phl025/ESP32_RC_Controller/document/pictures/ESP32_RC_Controler_004.jpg

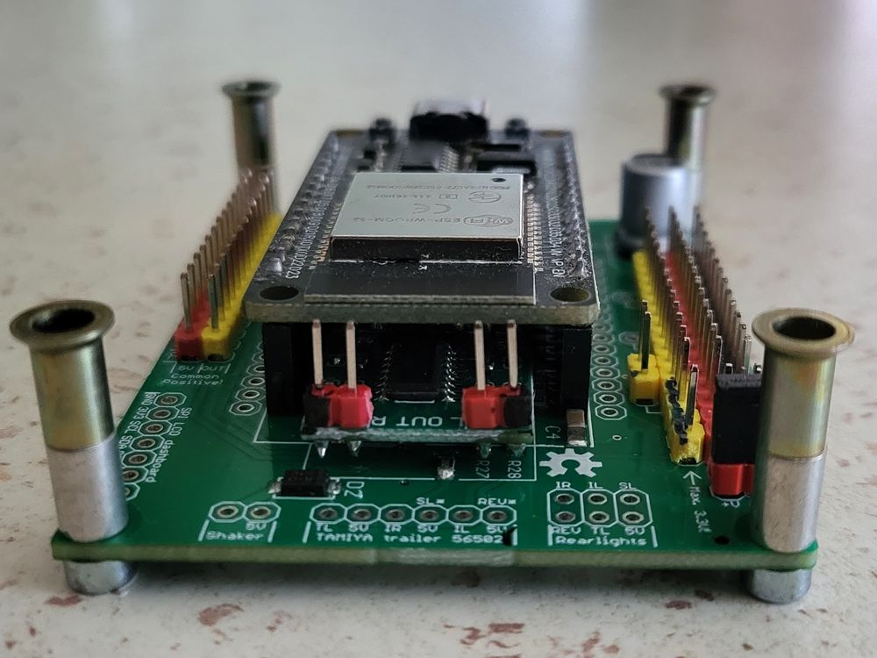
document/pictures/ESP32_RC_Controler_004.jpg
