phl025/ESP32_RC_Controller/document/pictures/ESP32_RC_Controler_006.jpg

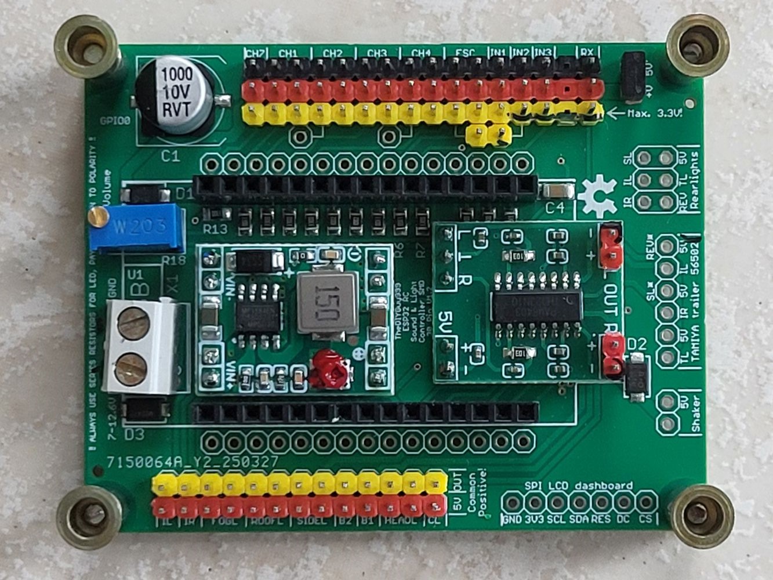
document/pictures/ESP32_RC_Controler_006.jpg
