phl025/ESP32_RC_Controller/src/src_ext/dashboard_frevic.h

#include "Arduino.h"
#include <TFT_eSPI.h>   // https://github.com/Bodmer/TFT_eSPI

/*
 * dashboard.h - Library to drive a 80x160px color LCD as rc truck dashboard
 *
 * https://github.com/Gamadril/Rc_Engine_Sound_ESP32
 * MIT License
 */

#ifndef DASHBOARD_H_FREVIC
#define DASHBOARD_H_FREVIC

#define SCREEN_WIDTH 160
#define SCREEN_HEIGHT 80

#define purple 0xEA16

// DEFINICIONES FREDY
#define SILVER 0xC618

#define FRAME_MAIN_X 80
#define FRAME_MAIN_Y 2
#define FRAME_MAIN_WITH 30
#define FRAME_MAIN_HEITH 14

#define FRAME_SUBMAIN_X 80
#define FRAME_SUBMAIN_Y 67
#define FRAME_SUBMAIN_WITH 60
#define FRAME_SUBMAIN_HEITH 12

#define INSTRUMENTOS_Y SCREEN_HEIGHT - 10;

#define GEAR_BOX_X 80
#define GEAR_BOX_Y 3 //(SCREEN_HEIGHT / 2) - 2
#define GEAR_BOX_WITH 12
#define GEAR_BOX_HEITH 20

// FIN DEFINICIONES FREDY

#define DEG2RAD 0.0174532925
#define SPEED_MIN 0
#define SPEED_MAX 120
#define RPM_MIN 0
#define RPM_MAX 500
#define FUEL_MIN 0
#define FUEL_MAX 100
#define ADBLUE_MIN 0
#define ADBLUE_MAX 100

#define SPEED_CIRCLE_CENTER_X 36
#define SPEED_CIRCLE_CENTER_Y 40
#define SPEED_CIRCLE_RADIUS 37
#define SPEED_NEEDLE_LENGTH 20
#define SPEED_CIRCLE_ANGLE_START -215 // -180 - 45
#define SPEED_CIRCLE_SEGMENTS 12
#define SPEED_CIRCLE_SEGMENT_ANGLE 20.83
#define SPEED_CIRCLE_ANGLE_END 35

#define RPM_CIRCLE_CENTER_X SCREEN_WIDTH - SPEED_CIRCLE_CENTER_X - 1
#define RPM_CIRCLE_CENTER_Y SPEED_CIRCLE_CENTER_Y
#define RPM_CIRCLE_RADIUS SPEED_CIRCLE_RADIUS
#define RPM_CIRCLE_ANGLE_START SPEED_CIRCLE_ANGLE_START
#define RPM_CIRCLE_SEGMENTS 12
#define RPM_CIRCLE_SEGMENT_ANGLE 20.83
#define RPM_CIRCLE_ANGLE_END 35

// no aplican
#define FUEL_CIRCLE_CENTER_X 30
#define FUEL_CIRCLE_CENTER_Y 60
#define FUEL_CIRCLE_RADIUS 14
#define FUEL_CIRCLE_ANGLE_START -202 // -180 - 22
#define FUEL_CIRCLE_SEGMENTS 16
#define FUEL_CIRCLE_SEGMENT_ANGLE 14
#define FUEL_CIRCLE_ANGLE_END \
    FUEL_CIRCLE_ANGLE_START + FUEL_CIRCLE_SEGMENTS *FUEL_CIRCLE_SEGMENT_ANGLE

#define ADBLUE_CIRCLE_CENTER_X SCREEN_WIDTH - 30
#define ADBLUE_CIRCLE_CENTER_Y 60
#define ADBLUE_CIRCLE_RADIUS 14
#define ADBLUE_CIRCLE_ANGLE_START -202 // -180 - 22
#define ADBLUE_CIRCLE_SEGMENTS 16
#define ADBLUE_CIRCLE_SEGMENT_ANGLE 14
#define ADBLUE_CIRCLE_ANGLE_END \
    ADBLUE_CIRCLE_ANGLE_START + ADBLUE_CIRCLE_SEGMENTS *ADBLUE_CIRCLE_SEGMENT_ANGLE

// #define INDICATOR_LEFT_CENTER_X SCREEN_WIDTH / 2 - 20
// #define INDICATOR_LEFT_CENTER_Y 9
// #define INDICATOR_RIGHT_CENTER_X SCREEN_WIDTH / 2 + 20
// #define INDICATOR_RIGHT_CENTER_Y 9
// Fredy
#define INDICATOR_LEFT_CENTER_X SCREEN_WIDTH / 2 - 14
#define INDICATOR_LEFT_CENTER_Y 7 // 8

#define INDICATOR_RIGHT_CENTER_X SCREEN_WIDTH / 2 + 14
#define INDICATOR_RIGHT_CENTER_Y 7 // 8

// CUSTOM COLOR DEFINITIONS
// http://www.rinkydinkelectronics.com/calc_rgb565.php
#define offColor 0x2104 // indicators off (very dark grey)
#define backColor 0x0026
#define gaugeColor 0x055D
#define dataColor 0x0311
#define purple 0xEA16
#define needleColor 0xfa29 //The color of the speed and RPM indicator needles (light red for better visibility)

const uint8_t LOW_BEAM_ICON[7][13] PROGMEM = {
    {1, 1, 0, 0, 0, 0, 0, 0, 0, 0, 0, 1, 1},
    {0, 1, 1, 1, 1, 0, 0, 0, 1, 1, 1, 1, 0},
    {0, 0, 1, 0, 1, 1, 0, 1, 1, 0, 1, 0, 0},
    {1, 1, 1, 0, 0, 1, 0, 1, 0, 0, 1, 1, 1},
    {0, 0, 1, 0, 1, 1, 0, 1, 1, 0, 1, 0, 0},
    {0, 1, 1, 1, 1, 0, 0, 0, 1, 1, 1, 1, 0},
    {1, 1, 0, 0, 0, 0, 0, 0, 0, 0, 0, 1, 1}};

const uint8_t HIGH_BEAM_ICON[7][13] PROGMEM = {
    {0, 0, 0, 0, 0, 0, 0, 1, 1, 1, 1, 0, 0},
    {1, 1, 1, 1, 1, 0, 1, 1, 0, 0, 1, 1, 0},
    {0, 0, 0, 0, 0, 0, 1, 0, 0, 0, 0, 1, 1},
    {1, 1, 1, 1, 1, 0, 1, 0, 0, 0, 0, 0, 1},
    {0, 0, 0, 0, 0, 0, 1, 0, 0, 0, 0, 1, 1},
    {1, 1, 1, 1, 1, 0, 1, 1, 0, 0, 1, 1, 0},
    {0, 0, 0, 0, 0, 0, 0, 1, 1, 1, 1, 0, 0}};

const uint8_t FOG_LIGHT_ICON[7][13] PROGMEM = {
    {0, 0, 0, 1, 1, 0, 0, 1, 1, 1, 1, 0, 0},
    {0, 1, 1, 1, 0, 0, 1, 1, 0, 0, 1, 1, 0},
    {1, 0, 1, 0, 1, 0, 1, 0, 0, 0, 0, 1, 1},
    {0, 1, 1, 1, 0, 0, 1, 0, 0, 0, 0, 0, 1},
    {1, 0, 0, 0, 1, 1, 1, 0, 0, 0, 0, 1, 1},
    {0, 1, 1, 1, 1, 0, 1, 1, 0, 0, 1, 1, 0},
    {1, 0, 1, 0, 0, 0, 0, 1, 1, 1, 1, 0, 0}};

const uint8_t PUMP_ICON[6][7] PROGMEM = {
    {0, 1, 1, 1, 1, 0, 0},
    {0, 1, 0, 0, 1, 1, 0},
    {0, 1, 0, 0, 1, 0, 1},
    {0, 1, 1, 1, 1, 1, 0},
    {0, 1, 1, 1, 1, 0, 0},
    {1, 1, 1, 1, 1, 1, 0}};

/**
 * @brief Class acts as a wrapper around TFT_eSPI routines to draw dashboard elements.
 *
 */
class Dashboard
{
public:
    /**
     * Default constructor
     */
    Dashboard();

    /**
     * Performs initialization of the display, rotates the coordinate system of the screen
     * (0,0) is the upper left corner if the connector is on the top.
     * Draws static dashboard elements and sets all values to 0.
     */
    void init(uint8_t value);

    /**
     * Sets the state of the left turn signal.
     * @param on - true to show the signal, false to deactivate it
     */
    void setLeftIndicator(boolean on);

    /**
     * Sets the state of the right turn signal.
     * @param on - true to show the signal, false to deactivate it
     */
    void setRightIndicator(boolean on);

    /**
     * Sets the state of the low beam lights.
     * @param on - true to show the indicator, false to deactivate it
     */
    void setLowBeamIndicator(boolean on);

    /**
     * Sets the state of the high beam lights.
     * @param on - true to show the indicator, false to deactivate it
     */
    void setHighBeamIndicator(boolean on);

    /**
     * Sets the state of the fog lights.
     * @param on - true to show the indicator, false to deactivate it
     */
    void setFogLightIndicator(boolean on);

    /**
     * Sets the speed to show by rotating the needle to the right position.
     * @param value - speed value between SPEED_MIN and SPEED_MAX
     */
    void setSpeed(uint16_t value);

    /**
     * Sets the RPM to show by rotating the needle to the right position.
     * @param value - RPM value between RPM_MIN and RPM_MAX
     */
    void setRPM(uint16_t value);

    /**
     * Sets the fuel level to show by rotating the needle to the right position.
     * @param value - fuel value between FUEL_MIN and FUEL_MAX
     */
    void setFuelLevel(uint16_t value);

    /**
     * Sets the AdBlue level to show by rotating the needle to the right position.
     * @param value - AdBlue value between ADBLUE_MIN and ADBLUE_MAX
     */
    void setAdBlueLevel(uint16_t value);

    /**
     * Sets the gear to show.
     * @param value - -1 for R, 0 for N, > 0 for gear number
     */
    void setGear(int8_t value);
    void setVolt(float value, float threshold);

private:
    TFT_eSPI _tft = TFT_eSPI();

    void drawFrame();
    void drawArc(int16_t cx, int16_t cy, int16_t r, int16_t deg_start, int16_t deg_end,
                 uint32_t color);
    void drawSep(int16_t cx, int16_t cy, uint16_t len, int16_t deg_pos, uint16_t r, uint32_t color);
    void drawNeedle(int16_t cx, int16_t cy, uint16_t len, int16_t deg_pos, uint16_t radius_holder,
                    uint32_t color_needle);
    void drawLeftIndicator(uint32_t color);
    void drawRightIndicator(uint32_t color);
    void drawLowBeamIndicator(uint32_t color);
    void drawHighBeamIndicator(uint32_t color);
    void drawFogLightIndicator(uint32_t color);
    void drawSpeed(uint16_t value);
    void drawRPM(uint16_t value);
    void drawFuel(uint16_t value);
    void drawAdBlue(uint16_t value);
    void drawPump(uint16_t x, uint16_t y, uint32_t color);
    void drawGear(char gear);
    void drawVolt(float volt, float threshold);

    void drawIndicadorFr(int16_t cx, int16_t cy, uint16_t len, int16_t deg_pos,
                         uint16_t radius_holder, uint32_t color_needle,
                         int16_t deg_pos_ant, uint32_t color_needle_ant, uint16_t pVelocidad);
    void drawNumVel();
    void drawNumrpm();

    void drawLogo(int16_t x, int16_t y, const uint16_t *bitmap, int16_t w, int16_t h); //Frevic logo
    
    uint32_t _BROWN = _tft.color565(160, 115, 71);

    float lx[360]; // text of Speed gaouges
    float ly[360];

    float xf[12]; // text of Speed gaouges
    float yf[12];
};

#endif
// End of Vrevic dashboard
