phl025/ESP32_RC_Controller/src/vehicles/PoyaudRev.h

const unsigned int revSampleRate = 22050;
const unsigned int revSampleCount = 15334;
const signed char revSamples[] = {//0
1, 1, -1, -6, -8, -11, -13, -11, -14, -14, -12, -16, -17, -18, -16, -16, //16
-15, -10, -11, -9, -4, -2, -3, -1, 1, 1, 5, 6, 7, 10, 1, -4, //32
-4, -3, 3, 5, 8, 9, 5, 0, -2, -3, -8, -9, -6, -9, -13, -12, //48
-11, -12, -14, -14, -11, -10, -14, -13, -11, -13, -11, -13, -15, -15, -16, -14, //64
-12, -7, -4, -6, -11, -12, -12, -11, -8, -5, -1, -3, -3, -1, -3, -4, //80
-1, -7, -15, -18, -18, -11, -7, -9, -14, -18, -19, -13, -11, -9, -6, -9, //96
-14, -21, -20, -17, -17, -20, -29, -33, -30, -29, -32, -34, -34, -34, -34, -31, //112
-31, -31, -32, -35, -35, -38, -34, -28, -29, -29, -29, -29, -26, -14, -10, -6, //128
-5, -6, -1, 3, 7, 10, 8, 8, 9, 10, 14, 18, 22, 25, 23, 25, //144
28, 31, 30, 33, 34, 35, 36, 35, 36, 38, 34, 33, 37, 41, 43, 45, //160
43, 40, 40, 38, 41, 44, 46, 48, 46, 48, 49, 44, 38, 34, 35, 35, //176
31, 29, 22, 14, 12, 17, 22, 26, 30, 33, 36, 39, 38, 36, 33, 32, //192
31, 25, 17, 17, 22, 20, 17, 18, 17, 15, 16, 18, 15, 15, 11, 6, //208
7, 9, 4, 1, 0, -3, -6, -11, -9, -10, -17, -21, -20, -22, -22, -20, //224
-18, -19, -22, -20, -19, -22, -24, -25, -31, -37, -38, -34, -34, -37, -40, -44, //240
-45, -44, -41, -38, -41, -41, -41, -39, -39, -50, -51, -48, -47, -44, -40, -34, //256
-32, -29, -26, -23, -21, -19, -19, -23, -25, -29, -34, -34, -33, -33, -31, -26, //272
-21, -16, -12, -9, -6, -4, 1, 5, 9, 12, 13, 16, 20, 20, 18, 24, //288
29, 32, 37, 37, 33, 28, 27, 25, 26, 28, 28, 30, 34, 32, 27, 28, //304
33, 34, 28, 27, 28, 30, 30, 30, 26, 23, 25, 27, 29, 34, 32, 29, //320
28, 24, 19, 18, 17, 16, 15, 13, 9, 11, 19, 22, 17, 15, 15, 16, //336
19, 15, 9, 3, -1, -2, -4, -4, -9, -9, -5, -5, -1, -1, -4, -8, //352
-16, -19, -18, -18, -15, -17, -25, -30, -34, -38, -36, -31, -30, -33, -34, -36, //368
-35, -30, -28, -31, -33, -29, -22, -23, -29, -33, -35, -40, -42, -41, -34, -28, //384
-29, -33, -34, -33, -28, -24, -18, -7, -9, -13, -15, -18, -16, -13, -12, -11, //400
-13, -19, -25, -21, -16, -15, -12, -6, -5, -8, -10, -6, -6, -2, 8, 8, //416
5, 2, -6, -1, 3, 11, 19, 19, 20, 17, 17, 23, 21, 18, 19, 19, //432
21, 19, 16, 17, 13, 16, 19, 22, 29, 31, 27, 24, 19, 16, 16, 16, //448
20, 19, 14, 8, 3, 4, 6, 9, 7, 4, 0, -3, -5, -8, -9, -8, //464
1, 4, 1, -1, 1, 5, 5, 2, 1, -1, -3, -3, -3, -4, -9, -11, //480
-7, -5, -4, -3, 4, 6, 1, 3, 5, 10, 13, 14, 16, 14, 15, 19, //496
19, 18, 17, 13, 12, 15, 15, 14, 15, 10, 6, 7, 10, 15, 19, 22, //512
22, 24, 24, 16, 16, 19, 19, 14, 10, 16, 17, 13, 14, 11, 4, 9, //528
15, 20, 22, 19, 15, 19, 21, 19, 17, 15, 14, 14, 9, 9, 15, 15, //544
15, 17, 16, 17, 17, 9, 6, 5, 7, 6, 1, 3, 3, -2, -3, -2, //560
3, 9, 8, 2, -7, -13, -16, -19, -18, -17, -20, -24, -21, -24, -25, -22, //576
-22, -20, -18, -16, -17, -16, -14, -18, -19, -20, -23, -28, -27, -29, -34, -36, //592
-39, -36, -30, -29, -30, -38, -37, -32, -28, -21, -20, -22, -23, -28, -25, -22, //608
-19, -20, -22, -24, -27, -26, -25, -26, -30, -32, -30, -31, -28, -23, -24, -25, //624
-23, -18, -13, -8, -6, -9, -11, -8, -5, -2, -2, -4, -2, 0, -3, 0, //640
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
