phl025/ESP32_RC_Controller/src/vehicles/PoyaudStat.h

const unsigned int startSampleRate = 22050;
const unsigned int startSampleCount = 44366;
const signed char startSamples[] = {//0
-1, -1, -1, -1, 0, -1, -1, -2, 0, -1, -1, 1, -1, 1, -2, -1, //16
0, -1, 1, -2, 0, 0, 1, -2, -3, 2, -3, -1, 1, 0, 1, -3, //32
0, -2, 2, -2, -3, 2, -1, 0, -1, 0, -1, -3, 1, 0, 2, 1, //48
-2, 1, 0, 0, 1, 0, 0, -3, 0, -2, 0, 2, -3, 1, -1, 0, //64
-2, -1, 1, -3, 1, -4, 1, 1, -2, 0, -1, 1, -1, -1, 3, -1, //80
1, -1, 0, 3, 0, 1, -1, 0, 0, -2, 0, 0, -2, -1, 1, 1, //96
-1, 1, -1, -2, 2, 0, 0, -1, 0, 1, -2, 1, -1, 0, 0, -2, //112
1, -2, 0, 0, -2, -1, 1, 0, -2, 0, -1, -1, 1, -3, 0, 0, //128
-2, 0, -2, 2, -2, -3, 1, -2, 0, -1, -1, 0, -2, 0, -1, 1, //144
-1, -2, 1, -1, -1, -2, 1, 2, -2, 1, -3, 0, 0, -3, 2, -3, //160
-1, 0, -1, 2, -2, 0, -1, -1, 1, 1, 0, -2, 1, -1, -2, 1, //176
-2, 2, 1, -2, -2, 0, -2, 0, 1, -2, -1, -1, -1, 0, -1, 1, //192
0, -1, -2, -1, 2, -1, 0, 0, -1, 1, 0, 1, -2, -1, -1, -2, //208
1, 1, -1, 0, 1, 2, -1, 1, 0, -2, 1, -1, -1, -2, 1, 0, //224
-4, 1, -2, 0, 0, -3, 2, 0, 0, -1, -1, -1, -3, 0, 0, 0, //240
-2, -2, 0, -2, 1, -1, -3, 1, 0, 1, 0, -3, 3, -2, -3, 2, //256
-2, 3, 0, 0, 0, -1, 2, -2, 0, 0, 0, 0, 0, 0, -1, -1, //272
2, -1, 0, 1, -2, 1, 0, 0, 0, 0, 0, -1, 0, -1, 1, -1, //288
-2, -1, -1, -1, -3, -1, -5, -1, 1, -2, 0, -2, 0, -1, -2, 1, //304
-2, 0, -3, -1, 3, -4, -1, -1, -1, -1, -2, 1, 0, 0, 0, -1, //320
0, -1, 1, -2, 0, 2, 0, 1, -2, 0, 3, 0, -1, -2, 1, 0, //336
-3, 1, 1, -1, -1, 0, 0, -3, 0, -1, -2, -1, -2, -1, 1, -2, //352
-2, -1, -1, -1, -1, -1, -3, -1, 1, -1, -1, -3, 0, 0, -3, 0, //368
-1, 0, 0, -2, -1, 0, 0, 0, -1, -1, 1, -2, -1, 1, -2, 1, //384
1, 0, 1, -3, 0, 2, 0, 1, -1, 0, -1, 0, 0, 3, 3, -4, //400
-2, 2, -1, 1, 0, 1, 0, -2, 0, -2, -1, 0, 0, -1, 0, 0, //416
-1, -1, -1, 0, -2, 1, 1, -1, 0, 0, 3, -1, 0, 0, 0, 0, //432
-2, 1, 0, 0, -1, 2, 0, -1, 1, -2, 2, 1, -1, 0, 1, -1, //448
-2, 0, -1, 0, -1, 1, 1, -1, -1, -2, 1, 0, -3, 0, -1, -4, //464
1, -1, 0, 0, -1, -1, -3, -2, 0, 0, -2, -1, 0, -2, -1, 2, //480
-2, -1, 0, -1, 1, 0, 0, -2, 0, 0, -2, 1, 0, -2, 0, 0, //496
1, 0, -1, -1, 0, 1, 0, 0, 1, -1, 1, 1, -2, 1, 0, -1, //512
1, 0, -2, 2, -2, -2, 1, -2, 0, -2, -2, 0, -1, -1, -2, 1, //528
-2, -2, 1, -2, 1, -2, -1, 1, 0, 0, -2, 3, -1, -2, 2, -2, //544
3, -1, -1, 2, -1, 2, -2, 1, 2, -2, 0, -3, 1, 2, 0, 0, //560
-1, 0, 0, 1, 0, 0, -2, 0, 2, 0, -3, 0, 1, -1, 0, -2, //576
-2, -1, 0, 1, -1, -1, -2, -1, 1, 1, 0, -2, -1, -1, 3, -1, //592
-1, 2, -2, -1, -2, 0, 0, -2, -1, -3, -2, 0, 0, 1, -2, -2, //608
-2, 0, 1, -2, 3, -1, -2, 0, -1, 0, -1, 0, 1, -1, -1, -1, //624
0, 1, 1, -2, -1, 0, -1, -2, -4, -1, 4, -6, -3, 4, -5, -2, //640
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
