phl025/ESP32_RC_Controller/src/vehicles/PoyaudStop.h

const unsigned int startSampleRate = 22050;
const unsigned int startSampleCount = 99224;
const signed char startSamples[] = {//0
4, 3, -1, -3, -3, -3, -5, -6, -8, -13, -16, -16, -16, -15, -13, -9, //16
-8, -15, -15, -13, -10, -12, -19, -20, -18, -19, -21, -26, -30, -21, -16, -10, //32
-2, -3, -13, -13, -14, -14, -12, -13, -15, -14, -14, -12, -10, -12, -12, -16, //48
-20, -20, -16, -12, -16, -22, -25, -25, -18, -6, -2, 2, 2, -2, -1, -2, //64
-2, 1, 4, 6, 6, 12, 15, 13, 11, 6, 8, 8, 7, 5, -7, -18, //80
-15, -12, -8, -2, 1, 1, 4, 8, 10, 13, 18, 15, 10, 12, 17, 19, //96
15, 14, 11, 7, 7, 7, 0, -4, -2, 0, 0, -1, 0, 6, 5, 2, //112
4, 7, 9, 6, 6, 5, 3, 1, 2, 5, 6, 6, 7, 1, 1, 4, //128
5, 4, 4, -1, -4, -4, -1, 0, 1, 1, -1, -2, -3, -2, 0, -3, //144
-6, -7, -8, -8, -10, -13, -14, -15, -16, -10, -8, -7, -2, 1, -3, -7, //160
-4, -4, -7, -9, -5, -5, -6, -8, -14, -15, -10, -10, -9, -7, -4, -8, //176
-9, -3, -4, -8, -8, 0, 1, -1, -3, -7, -7, 4, 11, 12, 11, 12, //192
13, 13, 15, 18, 20, 19, 19, 18, 17, 20, 24, 24, 26, 26, 24, 26, //208
27, 24, 19, 20, 23, 21, 22, 23, 22, 21, 19, 20, 21, 22, 28, 30, //224
28, 27, 26, 30, 30, 26, 24, 24, 25, 27, 23, 17, 16, 18, 12, 9, //240
7, 5, 2, -2, -7, -10, -13, -14, -9, -5, -8, -11, -16, -20, -21, -21, //256
-21, -19, -17, -16, -16, -18, -19, -23, -21, -17, -19, -19, -21, -26, -27, -26, //272
-24, -25, -27, -29, -32, -34, -30, -29, -28, -28, -29, -24, -19, -18, -25, -28, //288
-23, -18, -19, -18, -20, -25, -25, -23, -22, -22, -24, -24, -20, -17, -15, -14, //304
-11, -6, -2, -3, -6, -8, -10, -15, -12, -9, -6, 2, 5, 5, 5, 5, //320
9, 10, 8, 10, 10, 14, 18, 16, 6, 4, 7, 12, 15, 15, 16, 13, //336
10, 16, 17, 18, 20, 17, 13, 10, 13, 19, 16, 17, 17, 15, 15, 15, //352
14, 12, 13, 15, 14, 9, 7, 7, 7, 2, -3, -4, -5, 1, 3, 1, //368
3, 2, 5, 7, 5, 7, 7, 3, -1, -7, -13, -14, -17, -18, -17, -15, //384
-13, -19, -22, -23, -25, -27, -28, -25, -25, -26, -27, -30, -29, -24, -18, -14, //400
-15, -16, -14, -12, -11, -13, -16, -14, -13, -15, -15, -19, -24, -18, -14, -15, //416
-13, -10, -11, -13, -9, -11, -14, -12, -7, -3, -5, -2, 3, 3, 3, -2, //432
-2, 6, 7, 4, 1, -1, -1, -1, 2, 1, 3, 7, 6, 6, 6, 11, //448
12, 13, 16, 19, 23, 25, 24, 19, 14, 16, 20, 19, 19, 18, 17, 21, //464
23, 25, 31, 33, 32, 29, 26, 27, 31, 33, 34, 39, 39, 42, 44, 43, //480
46, 45, 46, 47, 48, 49, 48, 43, 40, 41, 39, 38, 41, 39, 38, 38, //496
37, 35, 32, 31, 31, 25, 20, 19, 20, 22, 23, 23, 22, 14, 12, 14, //512
14, 8, 4, 7, 6, 3, -6, -11, -9, -10, -9, -10, -15, -17, -12, -10, //528
-10, -13, -18, -19, -17, -20, -20, -19, -23, -28, -33, -36, -35, -34, -33, -38, //544
-39, -33, -30, -31, -27, -26, -27, -27, -29, -30, -29, -31, -35, -36, -33, -32, //560
-36, -37, -36, -33, -31, -32, -34, -36, -36, -34, -32, -33, -36, -36, -39, -41, //576
-42, -43, -38, -33, -32, -33, -35, -32, -30, -30, -32, -31, -32, -33, -31, -25, //592
-22, -22, -21, -22, -25, -25, -20, -18, -24, -25, -24, -24, -23, -19, -14, -14, //608
-17, -16, -11, -4, 2, 10, 9, 3, 1, 1, 2, 1, 2, 1, -2, 2, //624
6, 10, 11, 9, 15, 19, 20, 21, 23, 20, 19, 22, 20, 19, 22, 23, //640
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
