phl025/ESP32_RC_Controller/src/0_Model.h

//
// Models settings
//

// Civelier : TX16S + RP3-H
#include "models/civelier.h"

// Boulogne Etaple : TX16S + ER4
//#include "models/boulogne.h"

// Boulogne Etaple : Test PPM
//#include "models/test_ppm.h"

// Dashboard -> see global.h for dashboard configuration
//#define STD_DASHBOARD
//#define FREVIC_DASHBOARD
//#define NAVY_DASHBOARD

//
// EOF
//
