phl025/ESP32_RC_Controller/src/objects/receiver/rxBase.h

//
// rxBase.h : RX_Reciver base class
//
// Author : PHL @2025

#ifndef RX_BASE_H
#define RX_BASE_H

//#include <Arduino.h>
#include <stdint.h>
// Objects
#include "objects/global.h"
#include "objects/receiver/RxChannel.h"
//#include "objects/receiver/RxMultiSwitch.h"

// RX Status
#define RX_READY_COUNT 20		// Number of good read to be ready (20 = 200ms with 10ms update)// PHL 2026-01
#define RXREADY 1
#define RXFAILSAFE -1
#define RX_COMMUNICATION_LOST -2

// Class definition (header)
class RxBase
{
// Data
public:
	RxChannel channel[MAX_CHANNELS + 1];	// RX channel objects
	//RxMSwitch mSwitch;
	//
	volatile bool new_data = false;			// New RX data present
	volatile bool ready = false;			// RX Ready (not Failsafe)
	volatile bool failSafe = true;			//
	volatile int16_t error = 0;				// Error code for debug
	volatile uint32_t delta_us_proccess;	// Delta time proccessed
	//
	///volatile uint8_t multi_switch = 0x0;	// Test for multi-switch decodeur (PHL)

protected:
	bool *rev_channel_;
	int *fs_channel_;
	int *int_channel_;
	//
	uint16_t nb_channels_ = MAX_CHANNELS;
	volatile uint32_t last_rx_time_diff_;	// Last time rx recived
	volatile uint32_t last_us_proccess_;	// Last time proccessed
	//
	volatile uint16_t readyCount_ = 0;		// RX Ready count (Added PHL 2026-01)
	//
	volatile uint32_t timelast_ = 0;
	volatile uint32_t last_good_read_ = 0;
	volatile uint32_t it_count_ = 0;		// Interrupt count for diagnostic
	volatile uint32_t rd_count_ = 0;		// Read count, for diagnostic
	
// Methodes
public:
	RxBase(int channels);
	RxBase(int channels, int* p_chFailSafe, int* p_chIntegrator, bool* p_chReversed);
	//
	virtual void updateChannels(uint32_t cur_us);
	void processRawChannels(uint32_t cur_us);
	uint32_t timeDiff (uint32_t cur, uint32_t last);
	//
	void setRawChannel(int channel, uint16_t value);
	uint16_t getRxChannel(int channel);
	bool Get_NewData();
	uint8_t getBuffer(int index) const {return 0;}
	uint8_t getBufferLen() const {return 8;}

	// Inline function
	inline int getNbChannels() const {return nb_channels_;}
	inline uint32_t GetItCount() const {return it_count_;}
	inline uint32_t GetRdCount() const {return rd_count_;}
	inline uint32_t GetLastProccess()  const {return last_us_proccess_;}
	inline uint16_t GetReadyCount()  const {return readyCount_;}
	// Multi switch (move to rxChannel)
	//inline bool getMultiSwitch(int bit) const {return ((multi_switch >> bit) & 0x01);}		// bitRead(mixVal, bit);}


protected :
	// Obsolete :
	void processFailSafe();

};
#endif

//
// EOF
//
