phl025/ESP32_RC_Controller/src/src_ext/AlfredoCRSF.h

#pragma once

#include <Arduino.h>
//#include <src/crc8.h>
//#include <src/crsf_protocol.h>
#include "crc8.h"
#include "crsf_protocol.h"

enum eFailsafeAction { fsaNoPulses, fsaHold };

class AlfredoCRSF
{
public:
    // Packet timeout where buffer is flushed if no data is received in this time
    static const unsigned int CRSF_PACKET_TIMEOUT_MS = 100;
    static const unsigned int CRSFFAILSAFE_STAGE1_MS = 300;
    //uint32_t rdCount;       // Add PHL, read counter
    //bool newRCData;         // Add PHL, new RC channels datas

    AlfredoCRSF();
    void begin(Stream& port);
    void update();
    void write(uint8_t b);
    void write(const uint8_t *buf, size_t len);
    void queuePacket(uint8_t addr, uint8_t type, const void *payload, uint8_t len);

    // Return current channel value (1-based) in us
    int getChannel(unsigned int ch) const { return _channels[ch - 1]; }
    int getRawChannel(unsigned int ch) const { return _raw[ch - 1]; }           // Add PHL
    const crsfLinkStatistics_t *getLinkStatistics() const { return &_linkStatistics; }
    const crsf_sensor_gps_t *getGpsSensor() const { return &_gpsSensor; }
    const crsf_sensor_vario_t *getVarioSensor() const { return &_varioSensor; }
    const crsf_sensor_baro_altitude_t *getBaroAltitudeSensor() const { return &_baroAltitudeSensor; }
    const crsf_sensor_attitude_t *getAttitudeSensor() const { return &_attitudeSensor; }
    bool isLinkUp() const { return _linkIsUp; }

    // Add PHL
    bool newChannelsPacket();
    uint8_t getBuffer(int index) const {return _rxBuf[index];}

private:
    Stream* _port;
    uint8_t _rxBuf[CRSF_MAX_PACKET_LEN+3];
    uint8_t _rxBufPos;
    Crc8 _crc;
    crsfLinkStatistics_t _linkStatistics;
    crsf_sensor_gps_t _gpsSensor;
    crsf_sensor_vario_t _varioSensor;
    crsf_sensor_baro_altitude_t _baroAltitudeSensor;
    crsf_sensor_attitude_t _attitudeSensor;
    uint32_t _baud;
    uint32_t _lastReceive;
    uint32_t _lastChannelsPacket;
    bool _newChannelsPacket;            // Add PHL, new channel packet revive
    bool _linkIsUp;
    int _raw[CRSF_NUM_CHANNELS];        // Add PHL, raw value 2^11 = [0..2048]
    int _channels[CRSF_NUM_CHANNELS];

    void handleSerialIn();
    void handleByteReceived();
    void shiftRxBuffer(uint8_t cnt);
    void processPacketIn(uint8_t len);
    void checkPacketTimeout();
    void checkLinkDown();

    // Packet RX Handlers
    void packetChannelsPacked(const crsf_header_t *p);
    void packetLinkStatistics(const crsf_header_t *p);
    void packetGps(const crsf_header_t *p);
    void packetVario(const crsf_header_t *p);
    void packetBaroAltitude(const crsf_header_t *p);
    void packetAttitude(const crsf_header_t *p);
    
};
