phl025/ESP32_RC_Controller/src/src_ext/crc8.cpp

//#include <src_ext/crc8.h>
#include "crc8.h"

Crc8::Crc8(uint8_t poly)
{
    init(poly);
}

void Crc8::init(uint8_t poly)
{
    for (int idx=0; idx<256; ++idx)
    {
        uint8_t crc = idx;
        for (int shift=0; shift<8; ++shift)
        {
            crc = (crc << 1) ^ ((crc & 0x80) ? poly : 0);
        }
        _lut[idx] = crc & 0xff;
    }
}

uint8_t Crc8::calc(uint8_t *data, uint8_t len)
{
    uint8_t crc = 0;
    while (len--)
    {
        crc = _lut[crc ^ *data++];
    }
    return crc;
}
